bartMarinissen/cad-mouse-mk2/firmware/src/controllers/SerialController.cpp

#include "controllers/SerialController.h"

#include <string.h>

#include "Config.h"

void SerialController::begin() {
  // Unconditional: the link carries the calibration protocol, not just
  // telemetry, so it has to come up whether or not anyone is watching.
  Serial.begin(115200);

  // The wait is a different question, and is purely for a human. It gives USB
  // CDC time to enumerate so early boot diagnostics have somewhere to land --
  // worth a second of boot time when someone is reading the port, worth
  // nothing when nobody is.
  if (Config::ENABLE_TELEMETRY) {
    delay(1000);
  }
}

void SerialController::update() {
  size_t budget = kDrainBudget;

  while (budget-- > 0 && Serial.available() > 0) {
    const int next = Serial.read();
    if (next < 0) {
      break;
    }
    const char c = static_cast<char>(next);

    if (c != '\n') {
      if (overflow_) {
        continue;  // still discarding the remains of an oversized line
      }
      if (pendingLen_ + 1 >= kMaxLine) {
        overflow_ = true;
        pendingLen_ = 0;
        continue;
      }
      pending_[pendingLen_++] = c;
      continue;
    }

    if (overflow_) {
      Serial.println("STATUS SERIAL_OVERFLOW");
      overflow_ = false;
      pendingLen_ = 0;
      continue;
    }

    // Tolerate CRLF from hosts and terminals that send it.
    while (pendingLen_ > 0 && pending_[pendingLen_ - 1] == '\r') {
      pendingLen_--;
    }
    pending_[pendingLen_] = '\0';

    if (pendingLen_ > 0) {
      memcpy(line_, pending_, pendingLen_ + 1);
      // One slot, most recent wins. If a line completes while an earlier one
      // is still unconsumed the older is dropped, which is fine for a
      // request/response protocol at human pace -- and better than the
      // alternative of pausing the drain, since states that ignore serial
      // (IdleState) would then let the receive buffer back up.
      ready_ = true;
    }
    pendingLen_ = 0;
  }
}

const char* SerialController::takeLine() {
  if (!ready_) {
    return nullptr;
  }
  ready_ = false;
  return line_;
}
